StrontiumGroup/8-channel-DAC/Lab Bus requirements/SubBusDriver/Box/OLD/Driver4BusV11Side.pdf

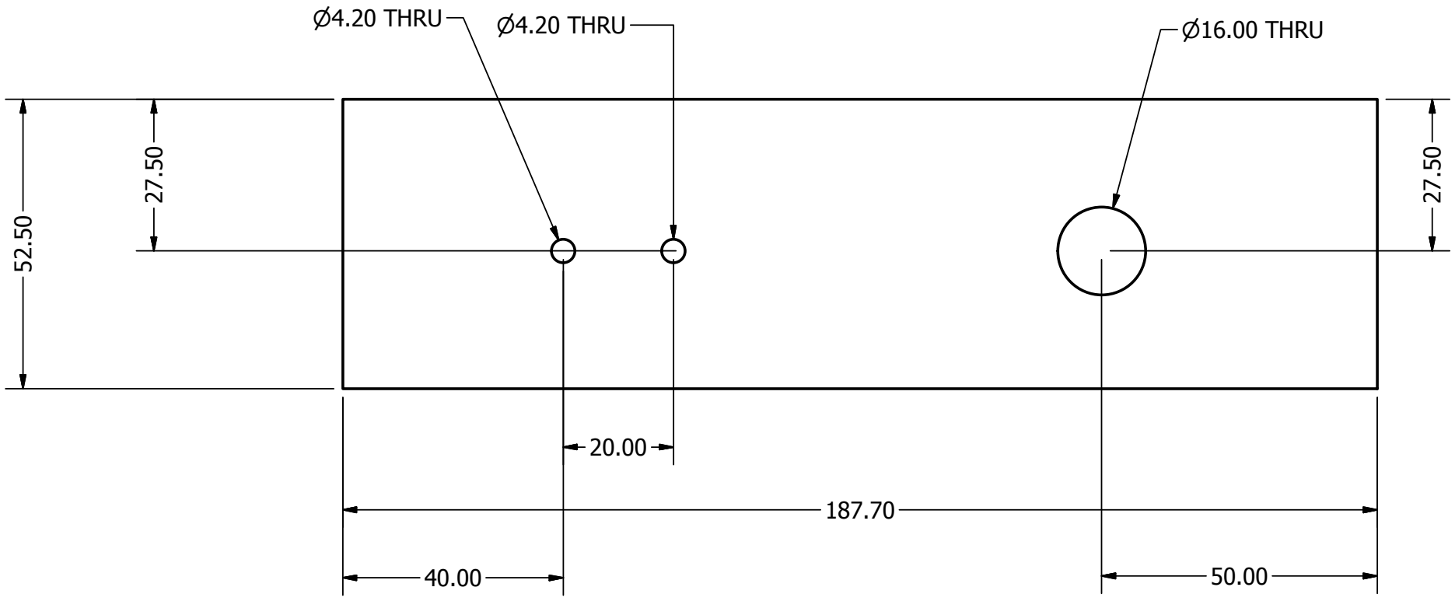
[picture p21: figure]

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
PRODUCED BY AN AUTODESK EDUCATIONAL PRODUCT

PRODUCED BY AN AUTODESK EDUCATIONAL PRODUCT

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
il | 2
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
