StrontiumGroup/8-channel-DAC/Pictures/SN00 proto modified/20221007_152033.jpg

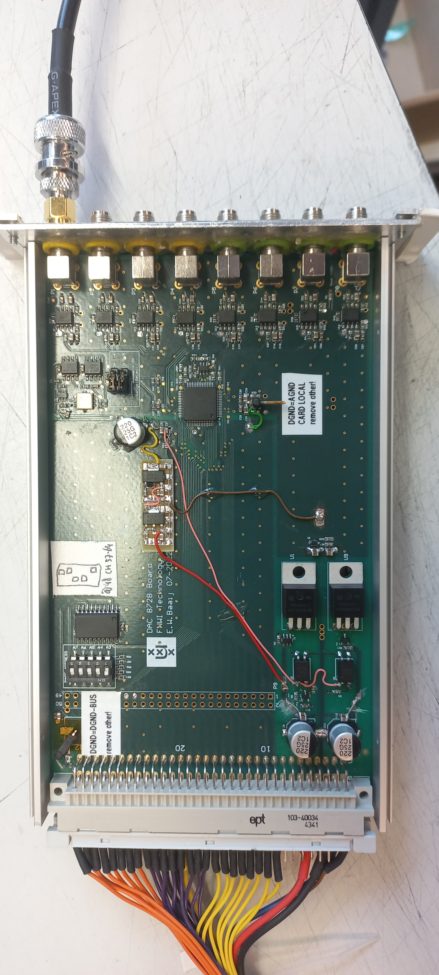
Pictures/SN00 proto modified/20221007_152033.jpg
