StrontiumGroup/8-channel-DAC/Pictures/SN00 proto modified/20221007_152048.jpg

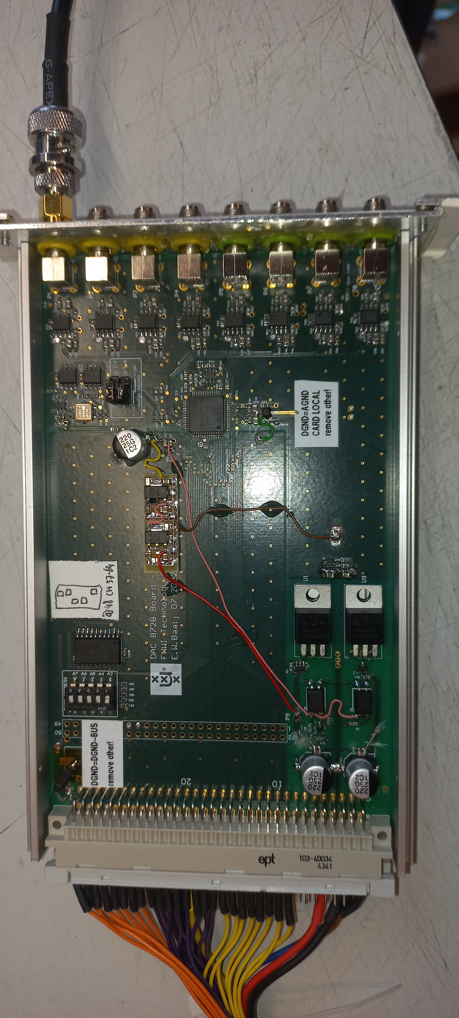
Pictures/SN00 proto modified/20221007_152048.jpg
