StrontiumGroup/8-channel-DAC/Lab Bus requirements/SubBusDriver/Box/OLD/Driver4BusV11TopCorrected.pdf

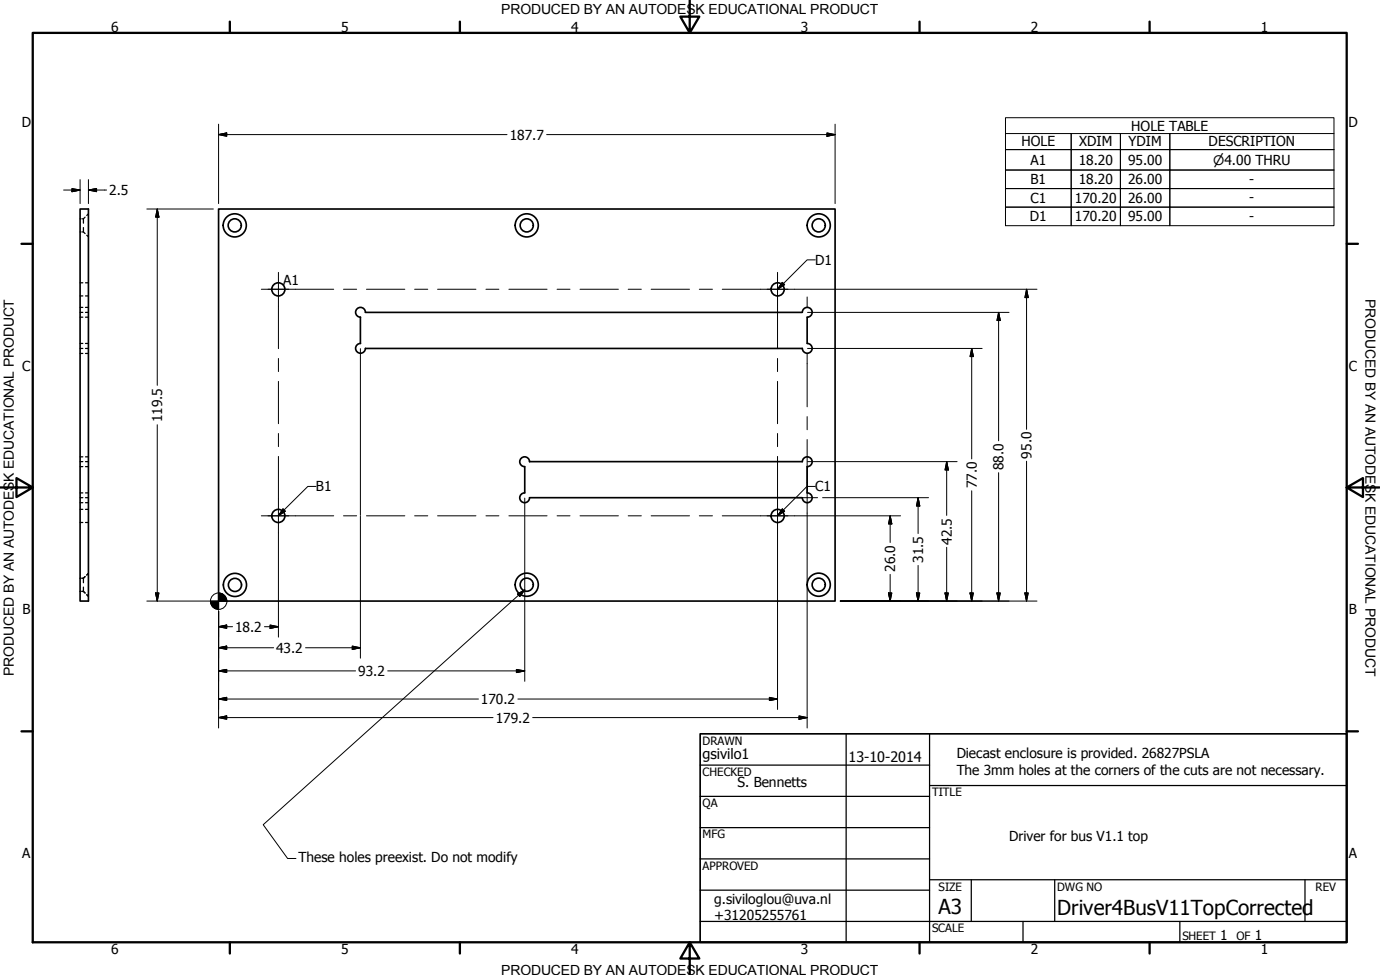
[picture p39: page 1]
TIO; P R O D U C E D B Y A N A U T O D E S K E D U C A TIO; SHEET 1 OF 1; DRAWN; CHECKED; MFG; APPROVED; gsivilo1; DWG NO Driver4BusV11TopCorrected; TITLE; SIZE A3; SCALE; REV; HOLE TABLE; HOLE; XDIM YDIM; DESCRIPTION; P4.00 THRU; S. Bennetts

PRODUCED BY AN AUTODESK EDUCATIONAL PRODUCT

Diecast enclosure is provided. 26827PSLA
The 3mm holes at the corners of the cuts are not necessary.

Driver for bus V1.1 top

These holes preexist. Do not modify

g.siviloglou@uva.nl
