StrontiumGroup/8-channel-DAC/Lab Bus requirements/SubBusDriver/Box/OLD/Driver4BusV11Top.pdf

P

P

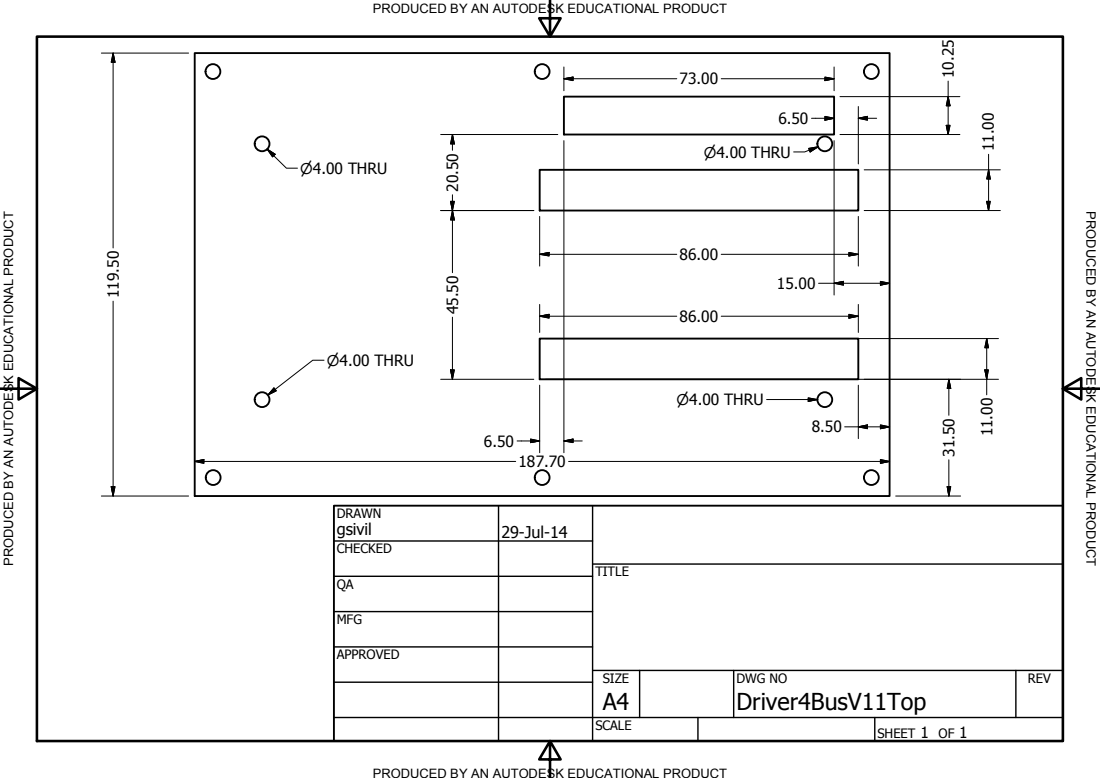
[picture p40: page 1]
TIO

PRODUCED BY AN AUTODESK EDUCATIONAL PRODUCT
